will127534/IMU_Array/IMUArray_ProcessingBoard/Code/imu_main/config.h

#ifndef CONFIG_H
#define CONFIG_H

// System Clock Configuration
#define SYS_CLOCK_KHZ (240 * 1000)

// Wi-Fi Configuration
//#define WIFI_SSID "Your_WiFi_SSID"
//#define WIFI_PASSWORD "Your_WiFi_Password"

#endif // CONFIG_H
