will127534/IMU_Array/IMUArray_ProcessingBoard/Code/imu_main/imu_cal.h

#ifndef CALIBRATION_H
#define CALIBRATION_H

#include <stdint.h>

#define NUM_IMUS 32

const float C_acc[NUM_IMUS][9] = {
    {0.9998105268f, 0.0000000000f, 0.0000000000f, -0.0000035826f, 0.9985158214f, 0.0000000000f, -0.0002904876f, 0.0022096304f, 0.9980619546f},
    {0.9981083284f, 0.0000000000f, 0.0000000000f, 0.0001800292f, 0.9974234437f, 0.0000000000f, -0.0009001902f, 0.0011584873f, 0.9981947339f},
    {0.9975054943f, 0.0000000000f, 0.0000000000f, -0.0000563137f, 1.0009442092f, 0.0000000000f, 0.0010859211f, 0.0008179942f, 0.9991929861f},
    {0.9991719477f, 0.0000000000f, 0.0000000000f, -0.0000246994f, 0.9994160188f, 0.0000000000f, 0.0007906832f, -0.0001609092f, 0.9982464843f},
    {0.9980636803f, 0.0000000000f, 0.0000000000f, 0.0001295855f, 1.0001301660f, 0.0000000000f, 0.0019155502f, 0.0003164042f, 0.9983481252f},
    {0.9976162187f, 0.0000000000f, 0.0000000000f, 0.0000177357f, 0.9990026287f, 0.0000000000f, 0.0018166327f, 0.0004597575f, 0.9980286598f},
    {0.9994714723f, 0.0000000000f, 0.0000000000f, -0.0001381889f, 0.9986973051f, 0.0000000000f, 0.0028323515f, 0.0009267418f, 0.9988161198f},
    {0.9982098908f, 0.0000000000f, 0.0000000000f, 0.0002830058f, 1.0002757048f, 0.0000000000f, 0.0027801793f, 0.0005984444f, 0.9982314472f},
    {0.9994890234f, 0.0000000000f, 0.0000000000f, -0.0000775737f, 0.9980249329f, 0.0000000000f, -0.0000921875f, 0.0013651257f, 0.9975211933f},
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
    {-0.0010145978f, -0.0035009731f, -0.0053749051f},
    {-0.0007949763f, -0.0024412169f, -0.0046362272f},
    {-0.0059816975f, -0.0033989911f, -0.0031795406f},
    {-0.0032402911f, -0.0037684096f, -0.0024057510f},
    {0.0000000000f, 0.0000000000f, 0.0000000000f}
};

#endif // CALIBRATION_H
